nichols89ben/Custom-3D-Printer-Enclosure-Modified/3D Renders/3D_Printer_Case_Render Front.png

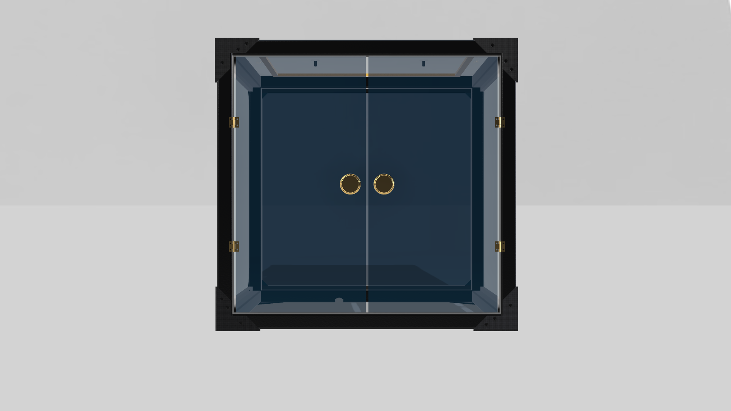
3D Renders/3D_Printer_Case_Render Front.png
