nichols89ben/Custom-3D-Printer-Enclosure-Modified/Build Pictures/3D Printer Case Front.jpeg

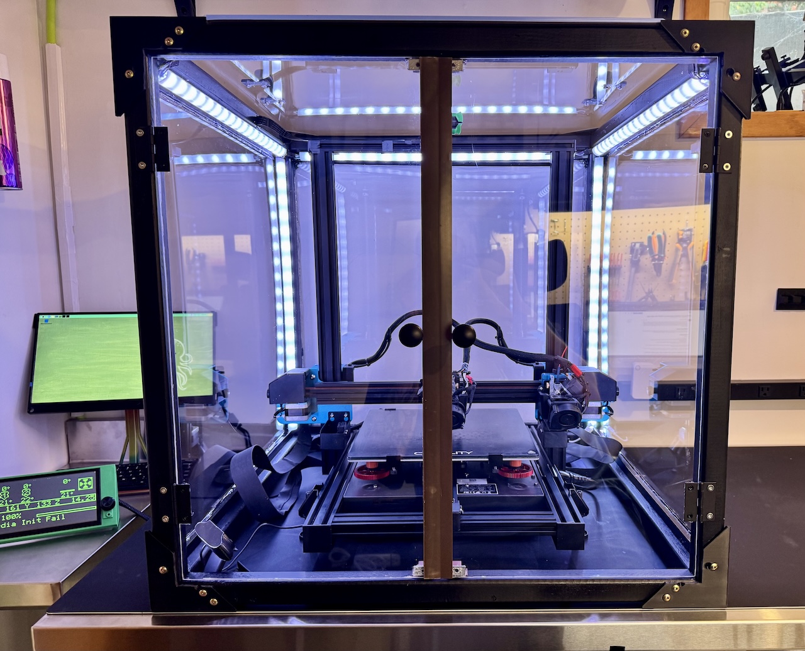
Build Pictures/3D Printer Case Front.jpeg
