nichols89ben/Custom-3D-Printer-Enclosure-Modified/Build Pictures/3D Printer Case Side 1.jpeg

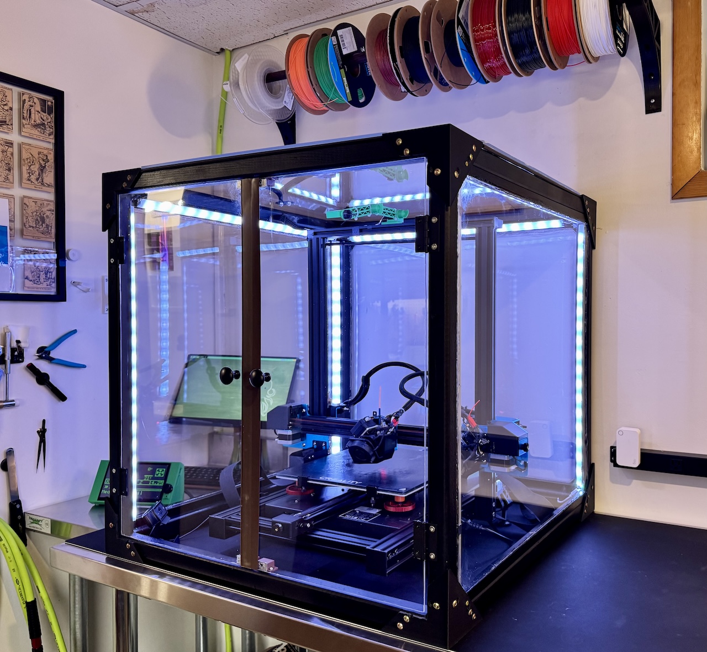
Build Pictures/3D Printer Case Side 1.jpeg
