nichols89ben/Custom-3D-Printer-Enclosure-Modified/Build Pictures/3D Printer Case Wood Gap FIller 1.jpeg

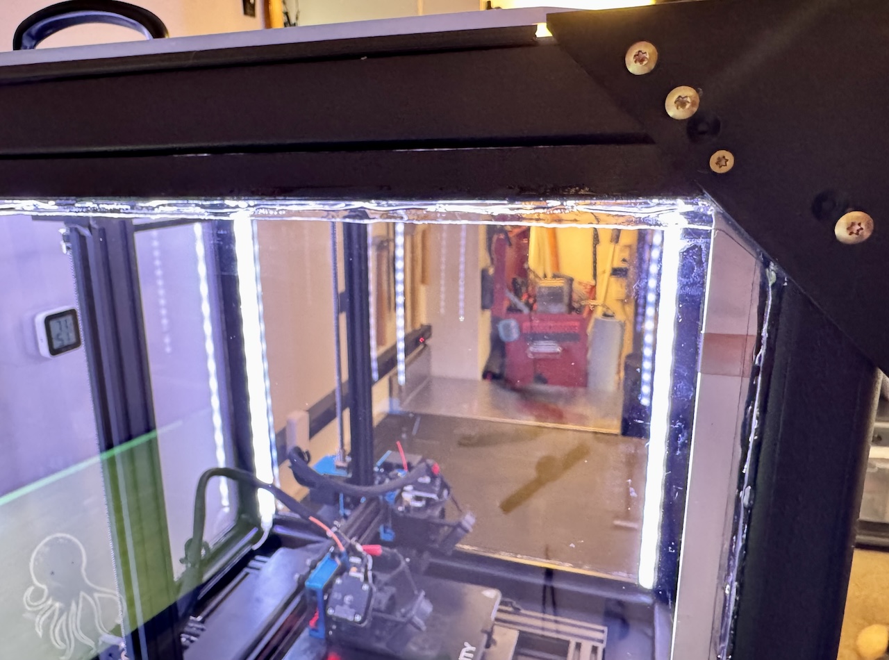
Build Pictures/3D Printer Case Wood Gap FIller 1.jpeg
