nichols89ben/Custom-3D-Printer-Enclosure-Modified/Build Pictures/3D Printer Case Wood Gap FIller 2.jpeg

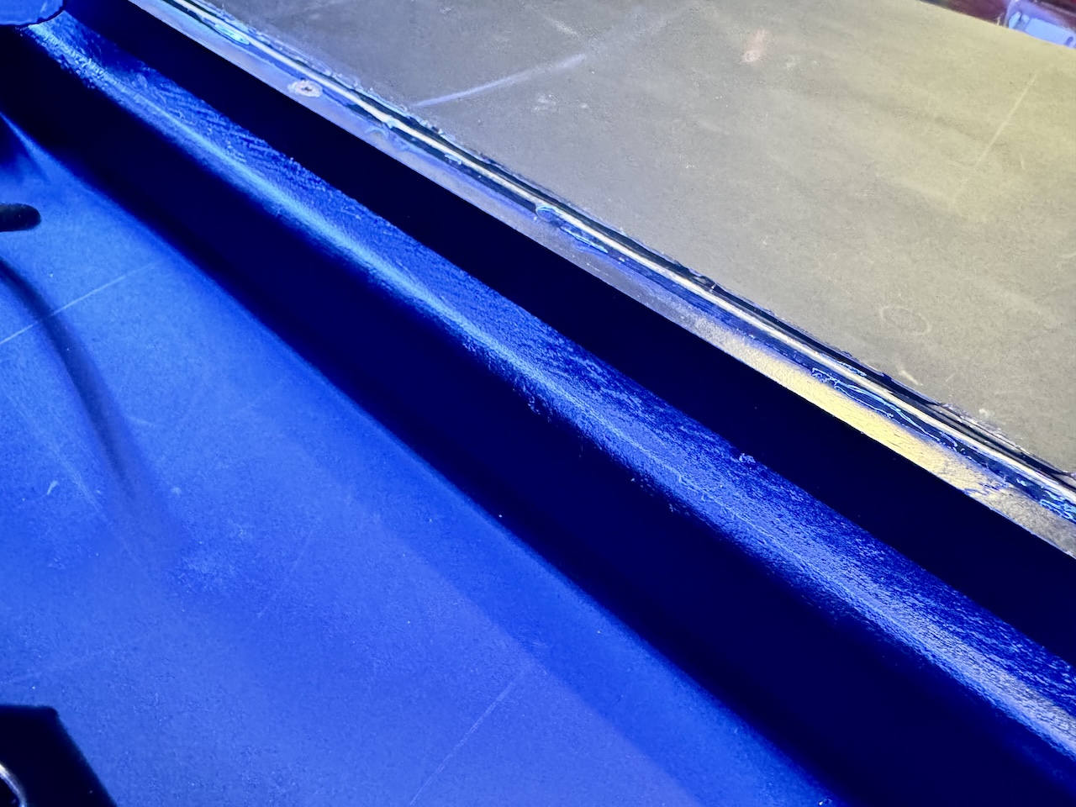
Build Pictures/3D Printer Case Wood Gap FIller 2.jpeg
